sdp8483/Tronxy_P802M_SKR_V1-3/AM8 Frame Upgrade/CAD/stl/z_stabilizer_right.stl

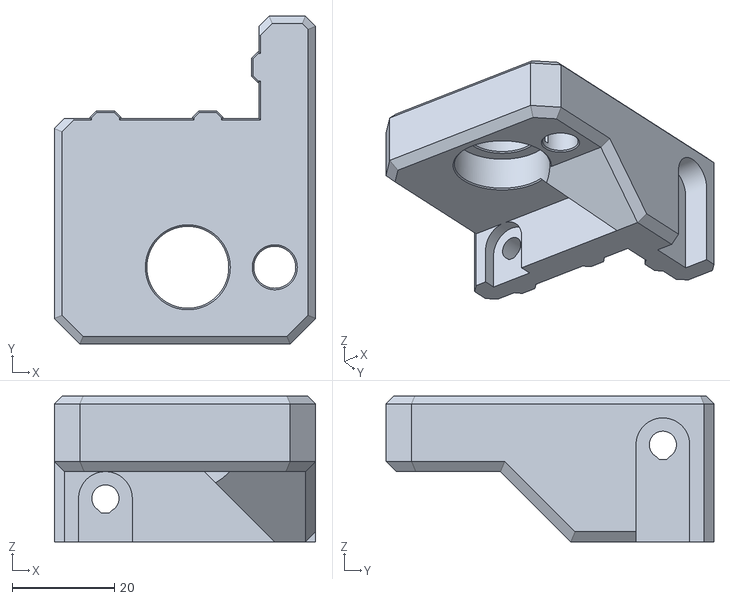
[picture p16: CAD file, 2023-12-26]
AM8 Frame Upgrade/CAD/stl/z_stabilizer_right.stl
51.1 x 64.1 x 28.5
