sdp8483/Tronxy_P802M_SKR_V1-3/AM8 Frame Upgrade/CAD/step/y_motor_mount.step

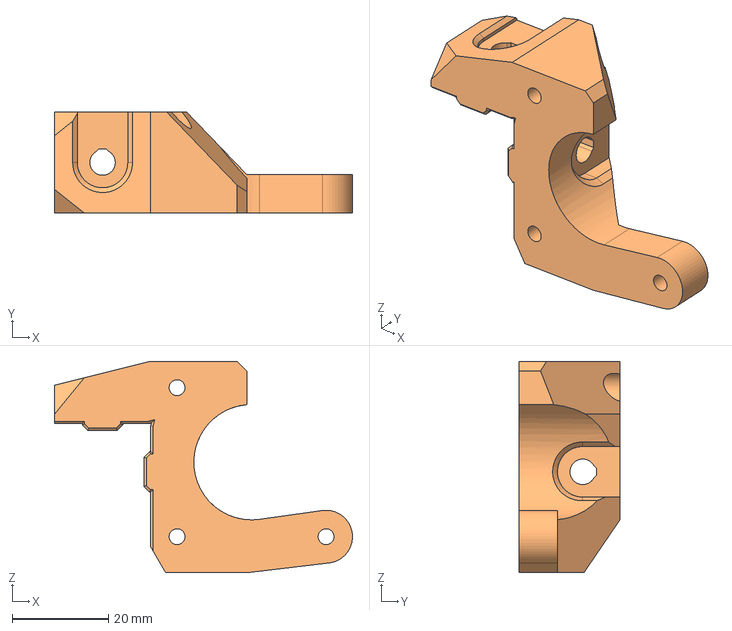
[picture p17: CAD file, 2020-06-11]
AM8 Frame Upgrade/CAD/step/y_motor_mount.step
62.0 x 21.0 x 44.0 mm
