sdp8483/Tronxy_P802M_SKR_V1-3/AM8 Frame Upgrade/CAD/stl/x_end_idler.stl

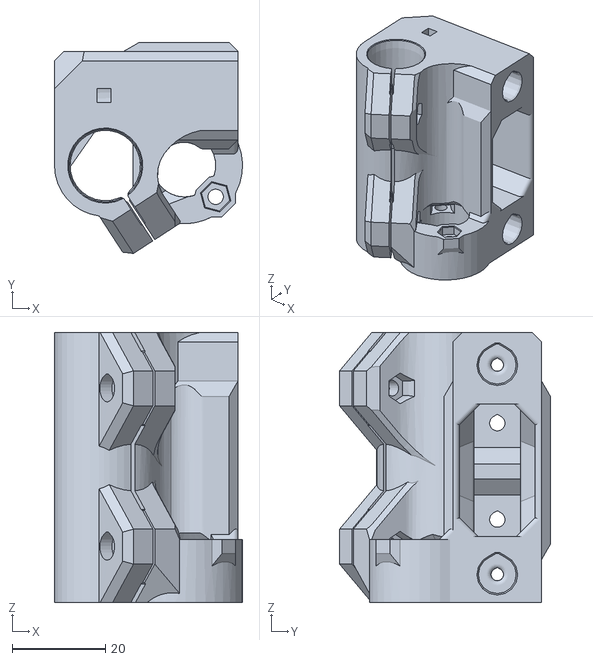
[picture p18: CAD file, 2020-07-21]
AM8 Frame Upgrade/CAD/stl/x_end_idler.stl
40.4 x 45.3 x 58.0
