sdp8483/Tronxy_P802M_SKR_V1-3/AM8 Frame Upgrade/CAD/step/y_idler.step

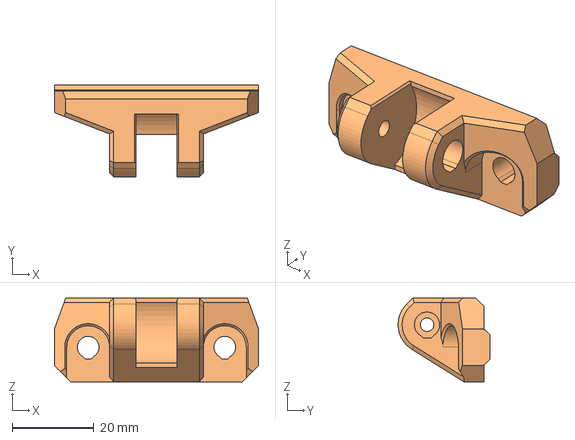
[picture p19: CAD file, 2020-06-11]
AM8 Frame Upgrade/CAD/step/y_idler.step
50.0 x 22.5 x 20.5 mm
