sdp8483/Tronxy_P802M_SKR_V1-3/AM8 Frame Upgrade/CAD/stl/psu_bracket_bottom.stl

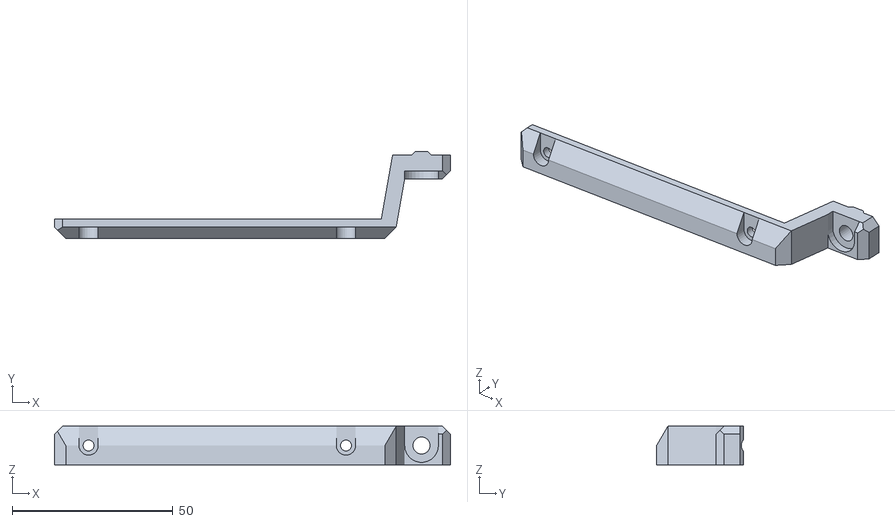
[picture p20: CAD file, 2020-07-15]
AM8 Frame Upgrade/CAD/stl/psu_bracket_bottom.stl
123.1 x 27.0 x 12.0
