sdp8483/Tronxy_P802M_SKR_V1-3/AM8 Frame Upgrade/CAD/step/Y_idler_bottom_Bear_RHD.stp

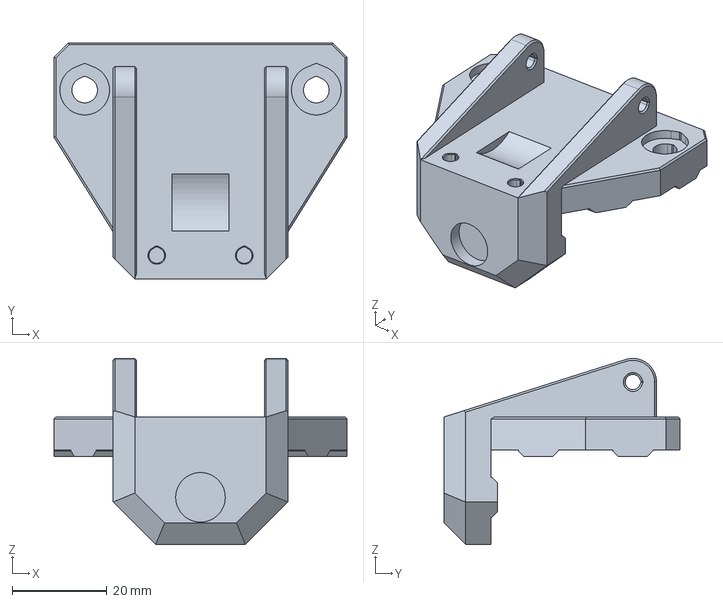
[picture p21: CAD file, 2020-06-11]
AM8 Frame Upgrade/CAD/step/Y_idler_bottom_Bear_RHD.stp
62.0 x 50.0 x 39.4 mm
