sdp8483/Tronxy_P802M_SKR_V1-3/AM8 Frame Upgrade/CAD/stl/psu_bracket_top.stl

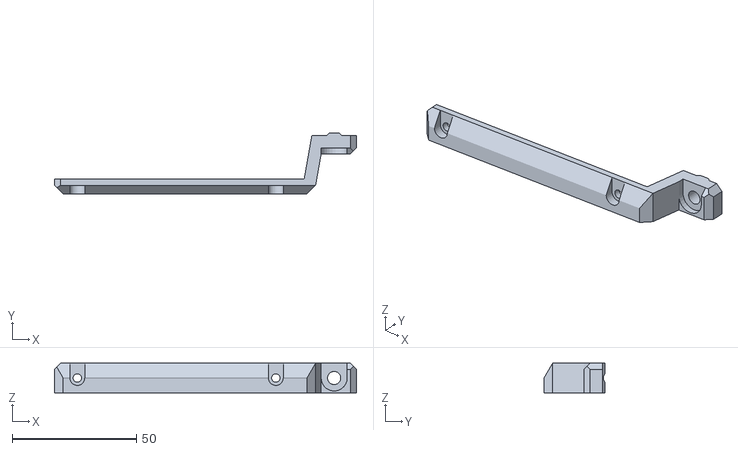
[picture p22: CAD file, 2020-07-15]
AM8 Frame Upgrade/CAD/stl/psu_bracket_top.stl
121.7 x 24.6 x 12.0
