sdp8483/Tronxy_P802M_SKR_V1-3/AM8 Frame Upgrade/CAD/stl/extruder_mount.stl

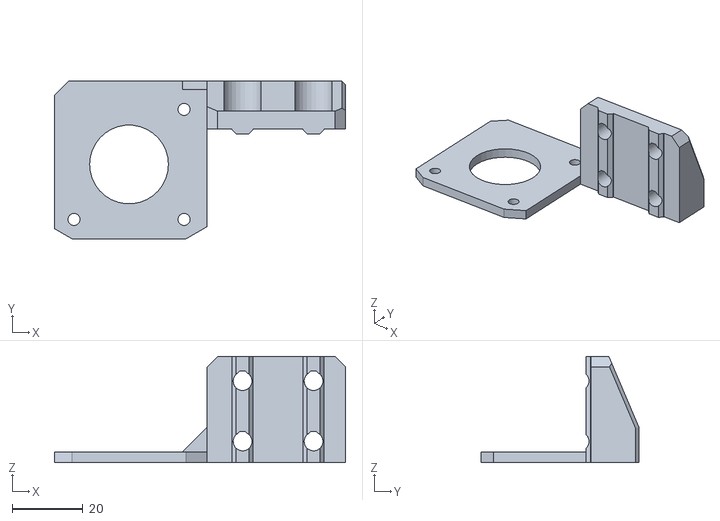
[picture p23: CAD file, 2020-07-12]
AM8 Frame Upgrade/CAD/stl/extruder_mount.stl
82.0 x 44.5 x 30.0
