sdp8483/Tronxy_P802M_SKR_V1-3/AM8 Frame Upgrade/CAD/step/z_motor_mount_left.step

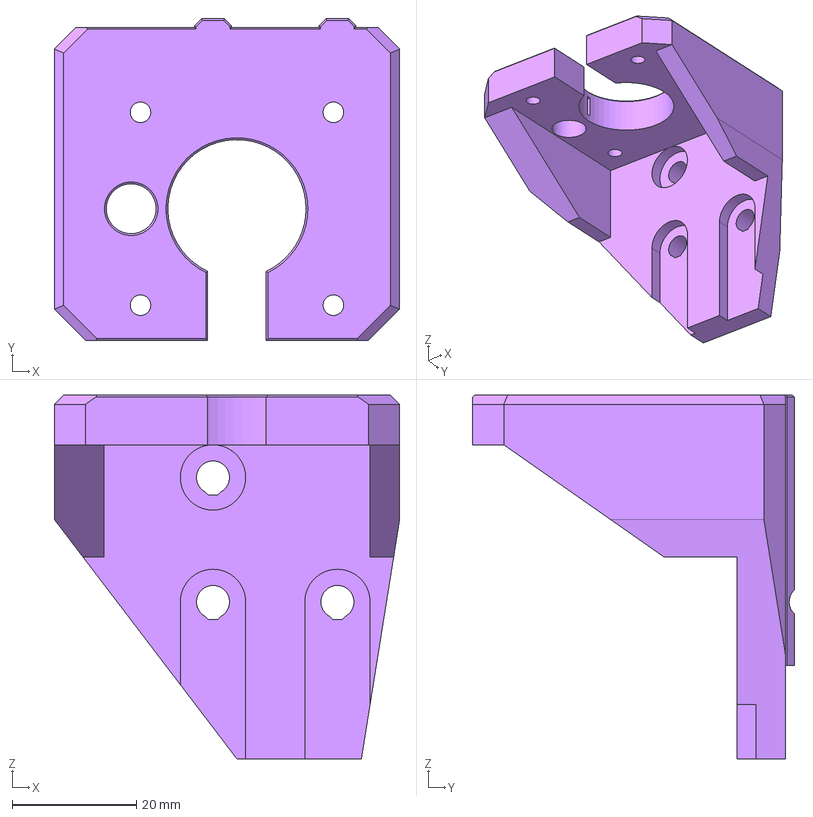
[picture p24: CAD file, 2020-06-09]
AM8 Frame Upgrade/CAD/step/z_motor_mount_left.step
55.5 x 51.7 x 58.5 mm
