sdp8483/Tronxy_P802M_SKR_V1-3/AM8 Frame Upgrade/CAD/stl/bl_touch_bracket.stl

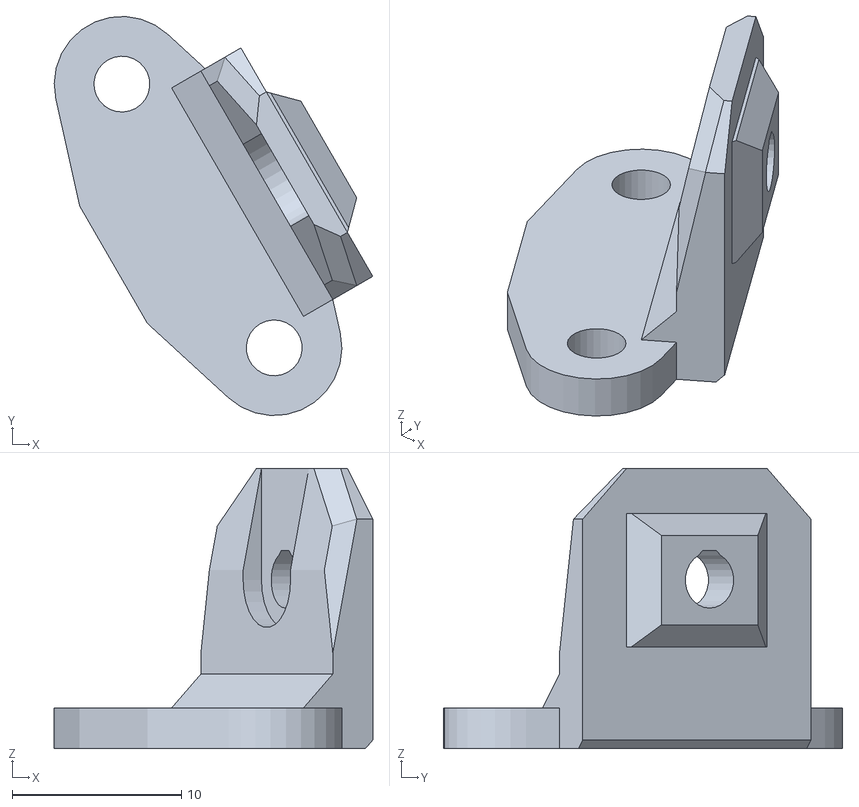
[picture p25: CAD file, 2020-07-11]
AM8 Frame Upgrade/CAD/stl/bl_touch_bracket.stl
18.8 x 23.6 x 16.6
