sdp8483/Tronxy_P802M_SKR_V1-3/AM8 Frame Upgrade/CAD/step/AM8.step

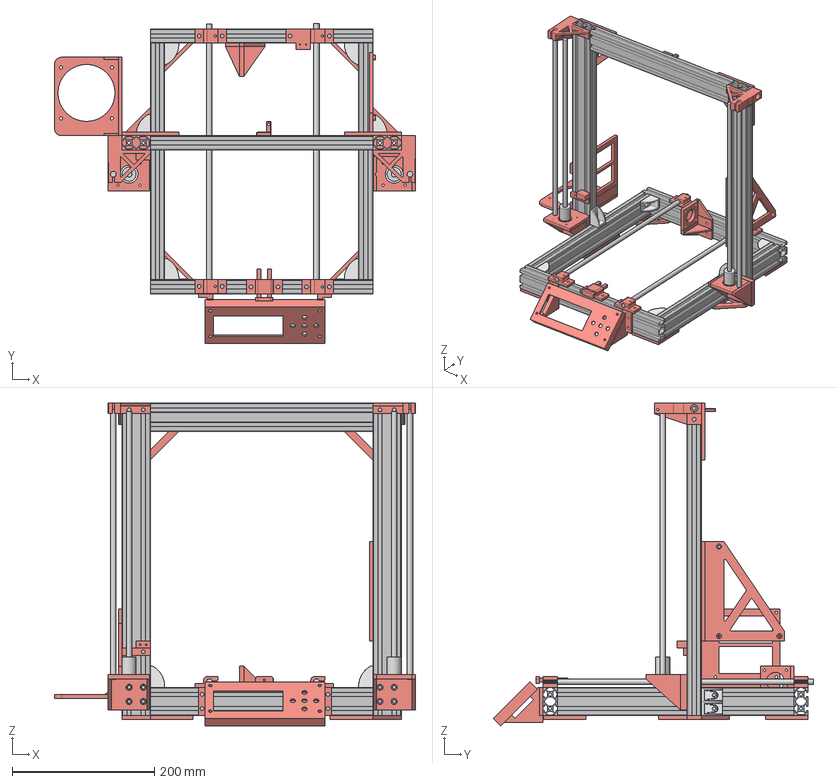
[picture p26: CAD file, 2020-06-09]
AM8 Frame Upgrade/CAD/step/AM8.step
508.0 x 450.6 x 454.5 mm
380mm x 4
Lead Screw x 2
Flex Coupler x 2
Vertical Mount
Vertical Mount(Mirror)
Vertical x 2
Bottom Horizontal 313 x 2
Bottom Right x 2
Topper 313
2040x2040 Slotted x 2
Bottom Tee x 2
Corner2020 x 4
Nema 17 Rear Mount
Y Rail Mount x 3
YMountWithEndstop
Z-Endstop
WithFan
PSU Mount (1)
Rod Holder
WireSupport
Rod Holder(Mirror)
_HBLFSNF5_b x 10
lcd_base
lcd_base(Mirror) (1)
Y Tensioner Block
Y Tensioner
