sdp8483/Tronxy_P802M_SKR_V1-3/AM8 Frame Upgrade/CAD/stl/bl_mount_fan.stl

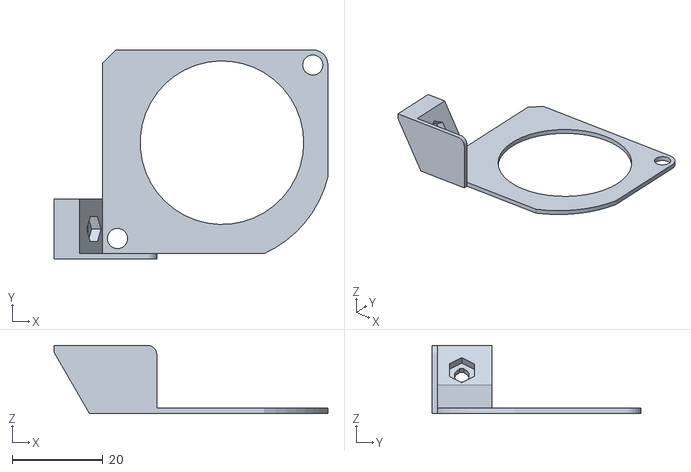
[picture p27: CAD file, 2020-07-11]
AM8 Frame Upgrade/CAD/stl/bl_mount_fan.stl
60.3 x 46.1 x 15.0
