sdp8483/Tronxy_P802M_SKR_V1-3/AM8 Frame Upgrade/CAD/stl/psu_cover.stl

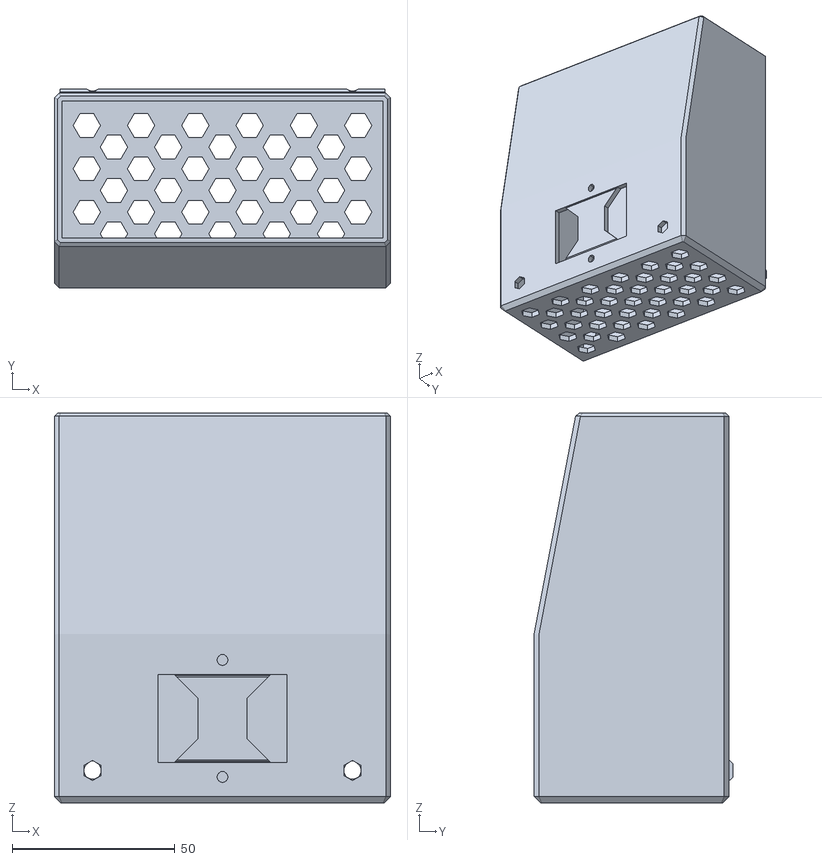
[picture p28: CAD file, 2020-07-10]
AM8 Frame Upgrade/CAD/stl/psu_cover.stl
103.5 x 61.2 x 120.0
