sdp8483/Tronxy_P802M_SKR_V1-3/AM8 Frame Upgrade/CAD/stl/psu_bracket.stl

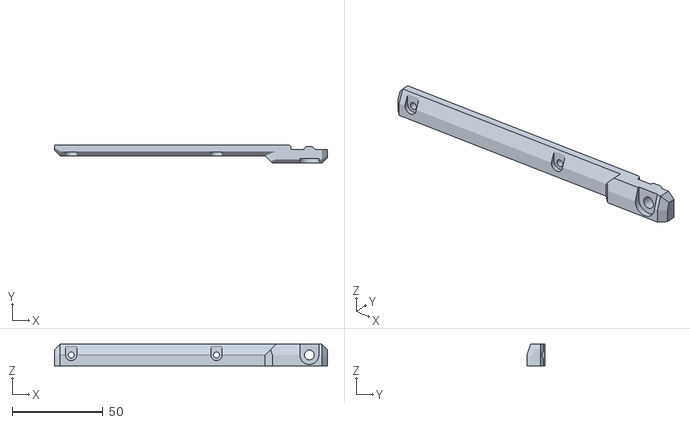
[picture p29: CAD file, 2020-07-10]
AM8 Frame Upgrade/CAD/stl/psu_bracket.stl
150.4 x 10.0 x 12.0
