sdp8483/Tronxy_P802M_SKR_V1-3/AM8 Frame Upgrade/CAD/stl/BTT_mount_bottom.stl

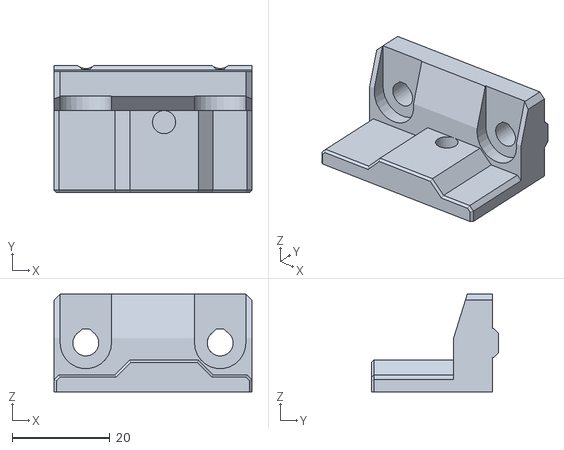
[picture p30: CAD file, 2020-07-02]
AM8 Frame Upgrade/CAD/stl/BTT_mount_bottom.stl
40.5 x 26.0 x 20.0
