sdp8483/Tronxy_P802M_SKR_V1-3/AM8 Frame Upgrade/CAD/stl/SKR_V14_Cover.stl

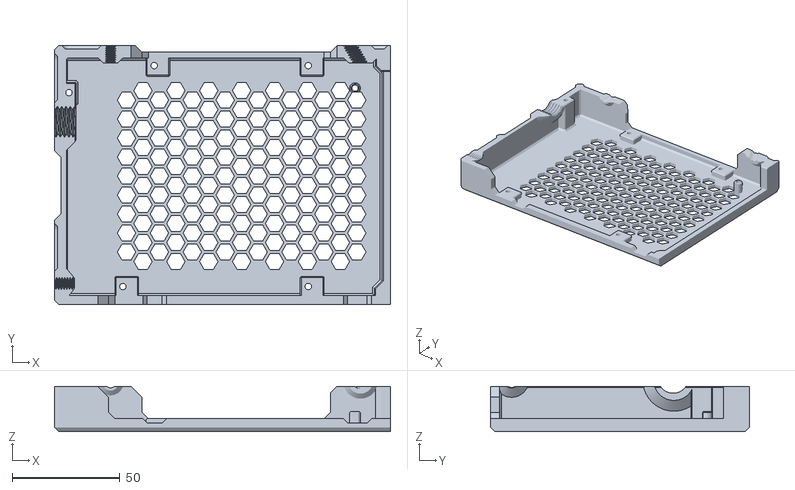
[picture p31: CAD file, 2020-07-02]
AM8 Frame Upgrade/CAD/stl/SKR_V14_Cover.stl
155.9 x 120.0 x 21.0
