sdp8483/Tronxy_P802M_SKR_V1-3/AM8 Frame Upgrade/CAD/stl/SKR_V14_Body.stl

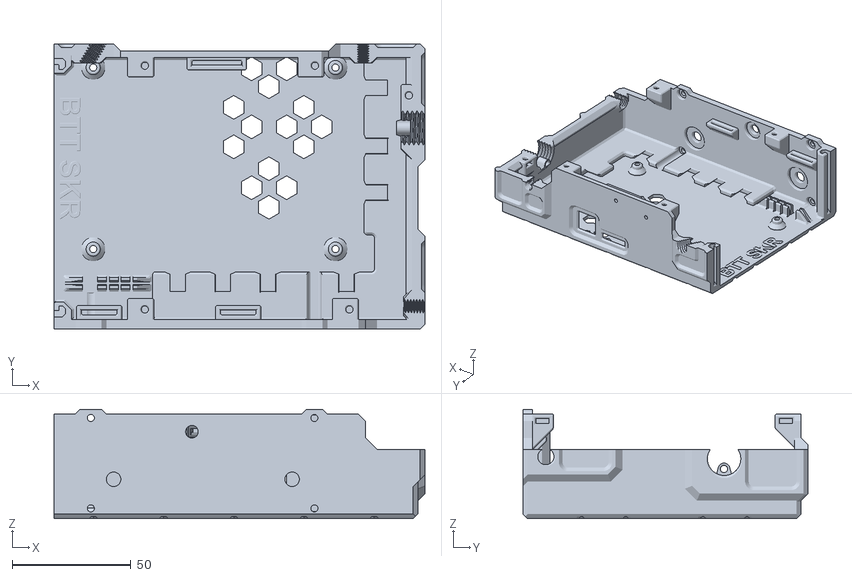
[picture p32: CAD file, 2020-07-02]
AM8 Frame Upgrade/CAD/stl/SKR_V14_Body.stl
156.0 x 120.0 x 46.0
