sdp8483/Tronxy_P802M_SKR_V1-3/AM8 Frame Upgrade/CAD/stl/lcd_support_a_modified.stl

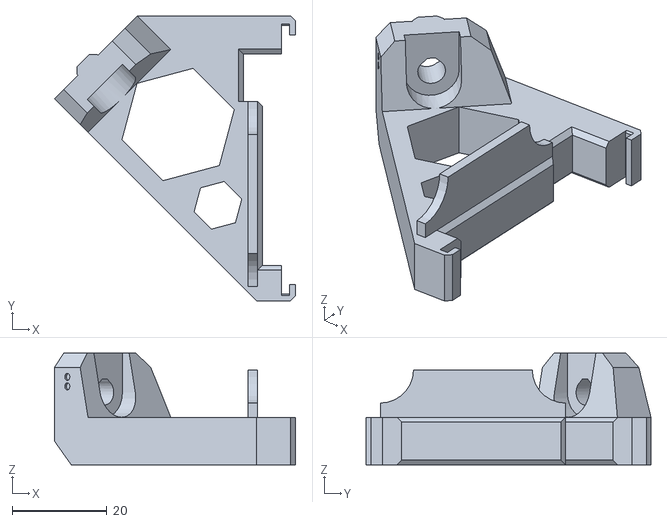
[picture p34: CAD file, 2020-06-16]
AM8 Frame Upgrade/CAD/stl/lcd_support_a_modified.stl
50.8 x 60.0 x 23.5
