sdp8483/Tronxy_P802M_SKR_V1-3/AM8 Frame Upgrade/CAD/stl/cable_guide_back_a.stl

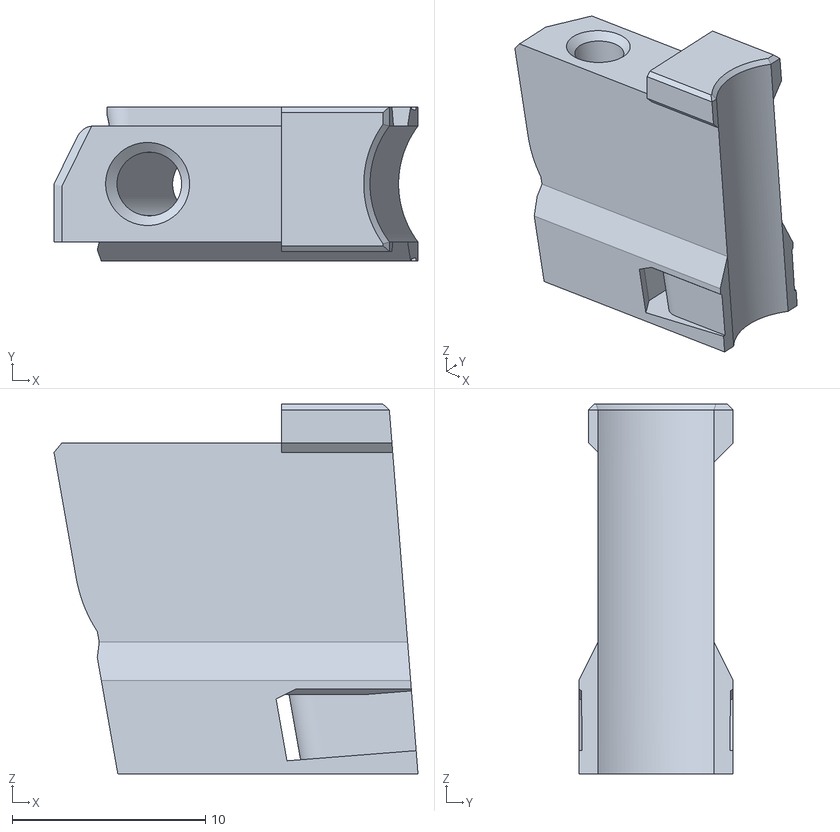
[picture p35: CAD file, 2020-06-16]
AM8 Frame Upgrade/CAD/stl/cable_guide_back_a.stl
18.9 x 8.00 x 19.1
