sdp8483/Tronxy_P802M_SKR_V1-3/AM8 Frame Upgrade/CAD/stl/extruder_cover.stl

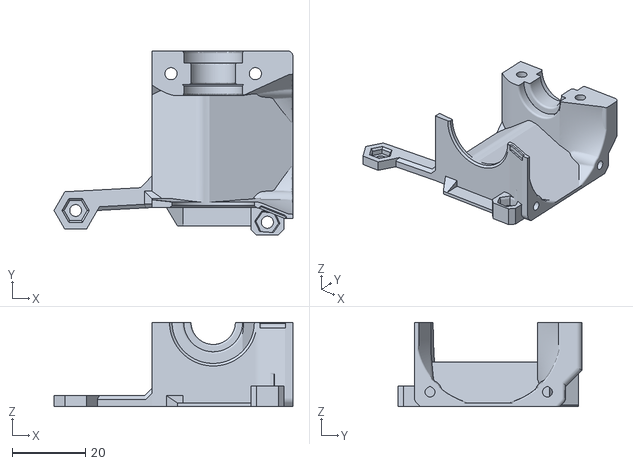
[picture p36: CAD file, 2020-06-16]
AM8 Frame Upgrade/CAD/stl/extruder_cover.stl
65.1 x 50.2 x 23.0
