sdp8483/Tronxy_P802M_SKR_V1-3/AM8 Frame Upgrade/CAD/stl/cable_guide_back_b.stl

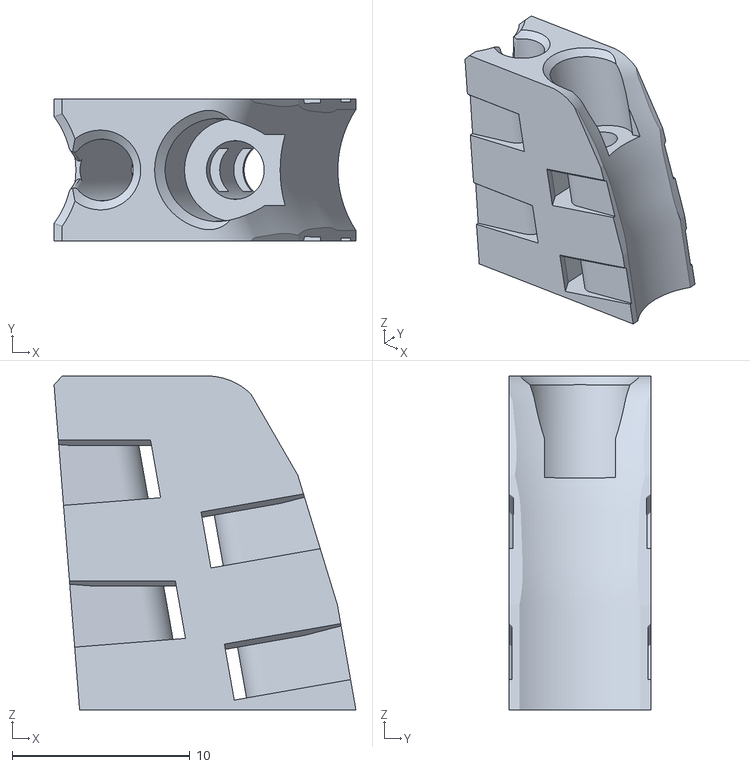
[picture p37: CAD file, 2020-06-16]
AM8 Frame Upgrade/CAD/stl/cable_guide_back_b.stl
17.0 x 8.00 x 18.8
