sdp8483/Tronxy_P802M_SKR_V1-3/AM8 Frame Upgrade/CAD/stl/hotend_mount_modified.stl

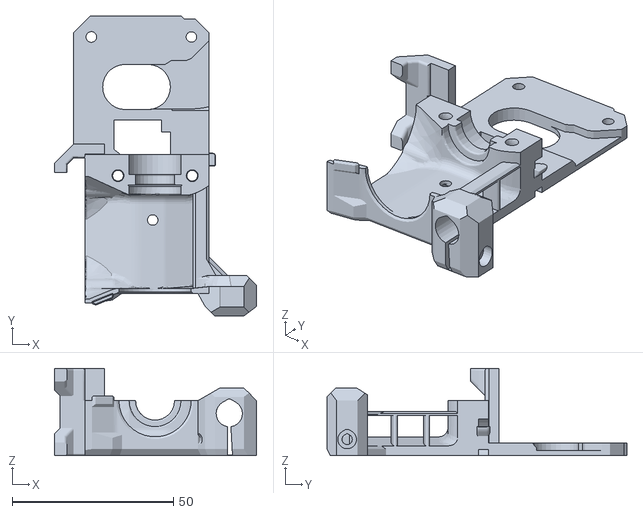
[picture p38: CAD file, 2020-06-14]
AM8 Frame Upgrade/CAD/stl/hotend_mount_modified.stl
62.8 x 93.0 x 27.0
