sdp8483/Tronxy_P802M_SKR_V1-3/AM8 Frame Upgrade/CAD/stl/x_carriage.stl

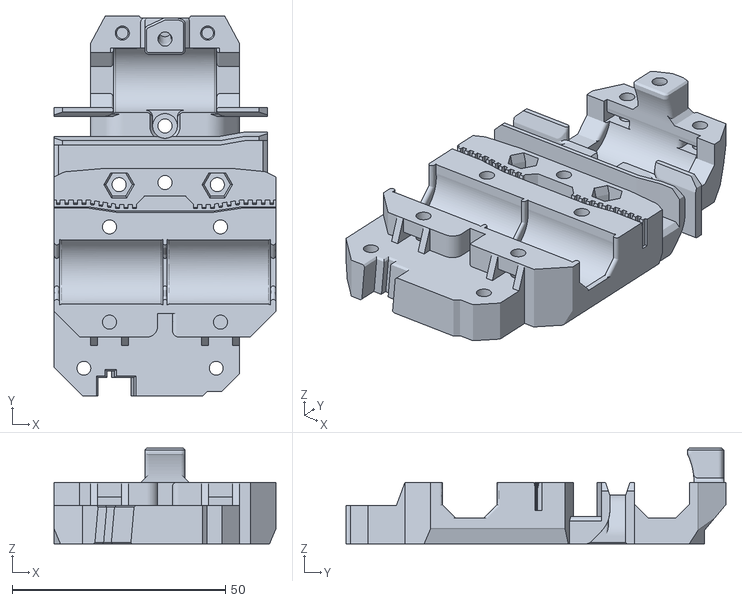
[picture p39: CAD file, 2020-06-14]
AM8 Frame Upgrade/CAD/stl/x_carriage.stl
52.0 x 89.0 x 22.4
