sdp8483/Tronxy_P802M_SKR_V1-3/AM8 Frame Upgrade/CAD/stl/2_Top_Corner_Plate.stl

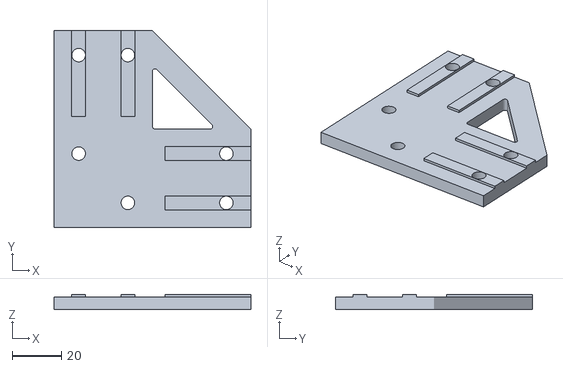
[picture p40: CAD file, 2020-06-14]
AM8 Frame Upgrade/CAD/stl/2_Top_Corner_Plate.stl
80.0 x 80.0 x 6.00
