sdp8483/Tronxy_P802M_SKR_V1-3/AM8 Frame Upgrade/CAD/stl/4_Bottom_Corner_Plate.stl

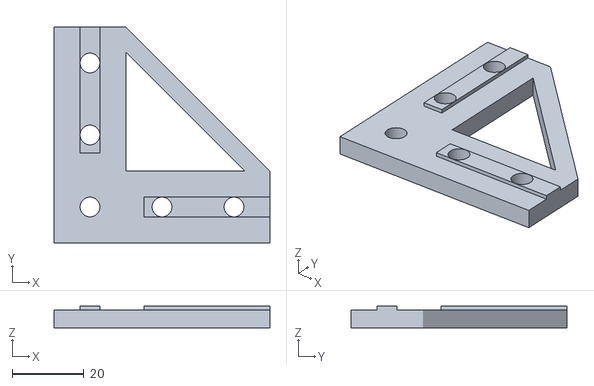
[picture p42: CAD file, 2020-06-14]
AM8 Frame Upgrade/CAD/stl/4_Bottom_Corner_Plate.stl
60.0 x 60.0 x 6.00
