sdp8483/Tronxy_P802M_SKR_V1-3/AM8 Frame Upgrade/CAD/stl/x_end_motor.stl

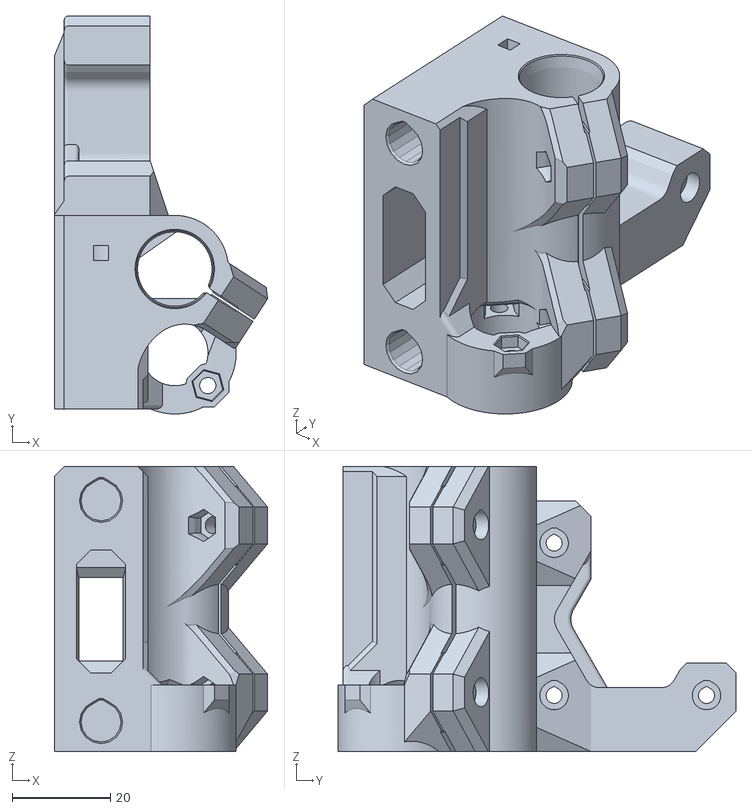
[picture p43: CAD file, 2020-06-14]
AM8 Frame Upgrade/CAD/stl/x_end_motor.stl
43.4 x 81.0 x 58.0
