sdp8483/Tronxy_P802M_SKR_V1-3/AM8 Frame Upgrade/CAD/stl/x_end_idler_tensioner.stl

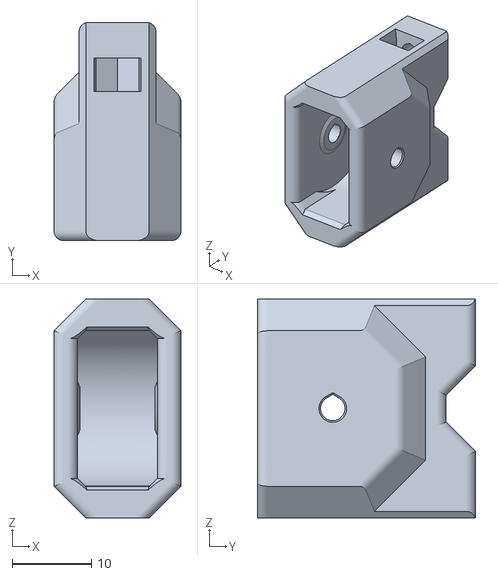
[picture p44: CAD file, 2020-06-14]
AM8 Frame Upgrade/CAD/stl/x_end_idler_tensioner.stl
16.0 x 27.5 x 27.6
