sdp8483/Tronxy_P802M_SKR_V1-3/AM8 Frame Upgrade/CAD/stl/x_carriage_back.stl

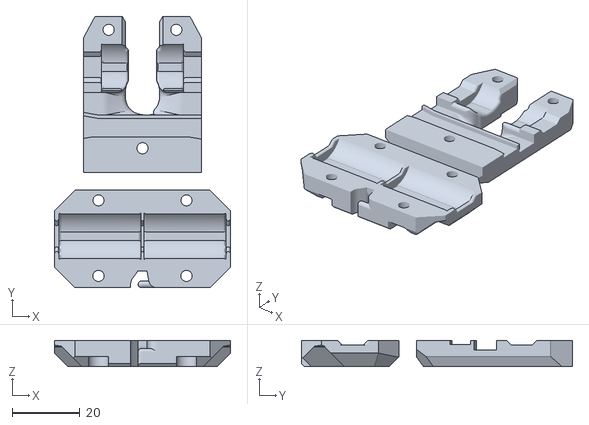
[picture p45: CAD file, 2020-06-14]
AM8 Frame Upgrade/CAD/stl/x_carriage_back.stl
52.0 x 80.2 x 7.80
