sdp8483/Tronxy_P802M_SKR_V1-3/AM8 Frame Upgrade/CAD/stl/y_belt_holder.stl

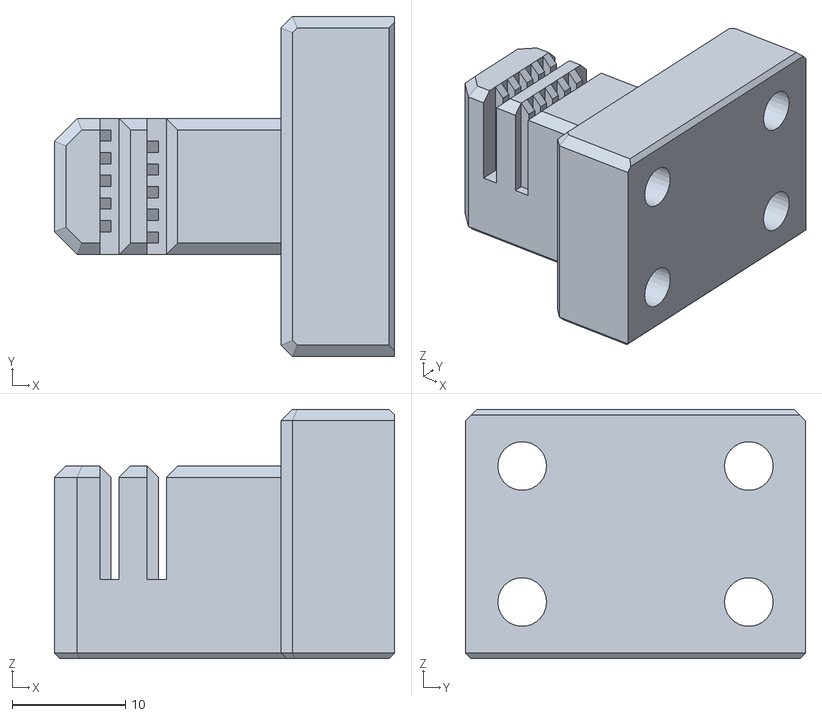
[picture p46: CAD file, 2020-06-13]
AM8 Frame Upgrade/CAD/stl/y_belt_holder.stl
30.0 x 30.0 x 22.0
