sdp8483/Tronxy_P802M_SKR_V1-3/AM8 Frame Upgrade/CAD/stl/y_rod_holder.stl

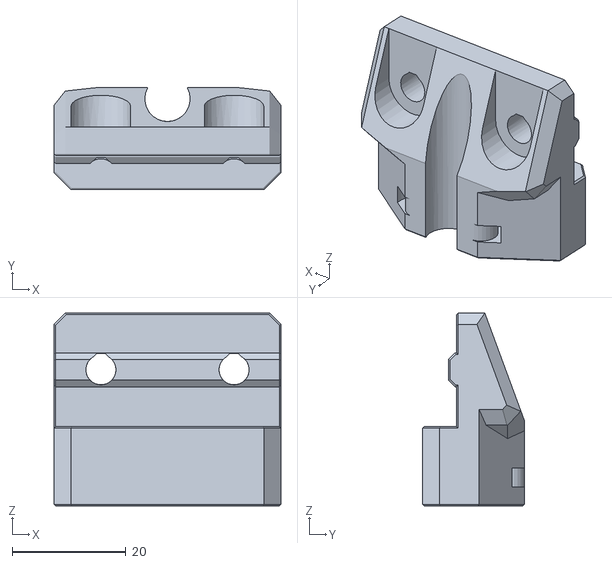
[picture p47: CAD file, 2020-06-12]
AM8 Frame Upgrade/CAD/stl/y_rod_holder.stl
40.0 x 18.0 x 34.0
