sdp8483/Tronxy_P802M_SKR_V1-3/AM8 Frame Upgrade/CAD/stl/y_idler_holder_Bear_RHD.stp

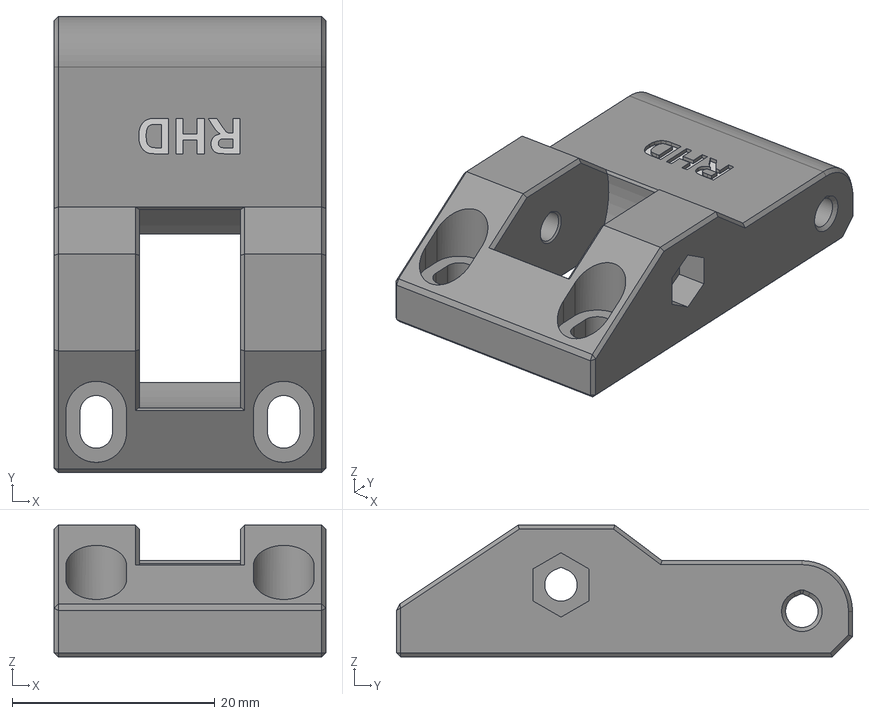
[picture p48: CAD file, 2020-06-11]
AM8 Frame Upgrade/CAD/stl/y_idler_holder_Bear_RHD.stp
26.8 x 45.0 x 13.0 mm
