sdp8483/Tronxy_P802M_SKR_V1-3/AM8 Frame Upgrade/CAD/stl/z_motor_mount_right.stl

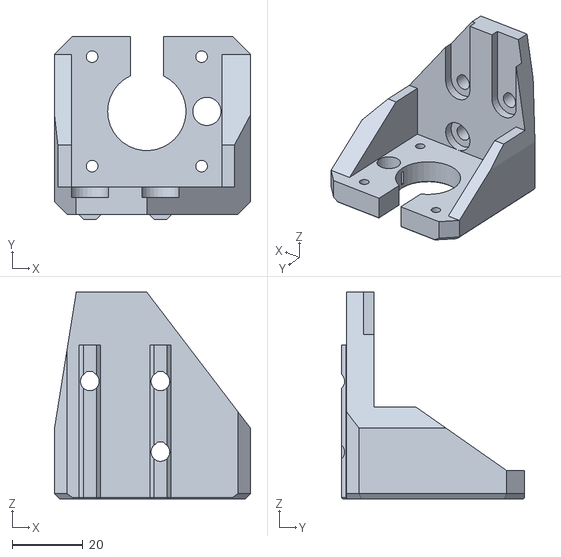
[picture p49: CAD file, 2020-06-09]
AM8 Frame Upgrade/CAD/stl/z_motor_mount_right.stl
55.5 x 51.7 x 58.5
